MindrustUK/Maltron_S_Edition/QMK Firmware/keyboards/mindrustuk/maltron_s_edition/mcuconf.h

// Copyright 2022 Mehmet Can (@MindrustUK)
// SPDX-License-Identifier: GPL-2.0-or-later
#pragma once

#include_next <mcuconf.h>

#undef STM32_PWM_USE_TIM3
#define STM32_PWM_USE_TIM3 TRUE

#undef STM32_SERIAL_USE_USART1
#define STM32_SERIAL_USE_USART1 TRUE

#undef STM32_I2C_USE_I2C1
#define STM32_I2C_USE_I2C1 TRUE
